buccia105/unity_game_controller/IMAGES/IMG_1095.JPG

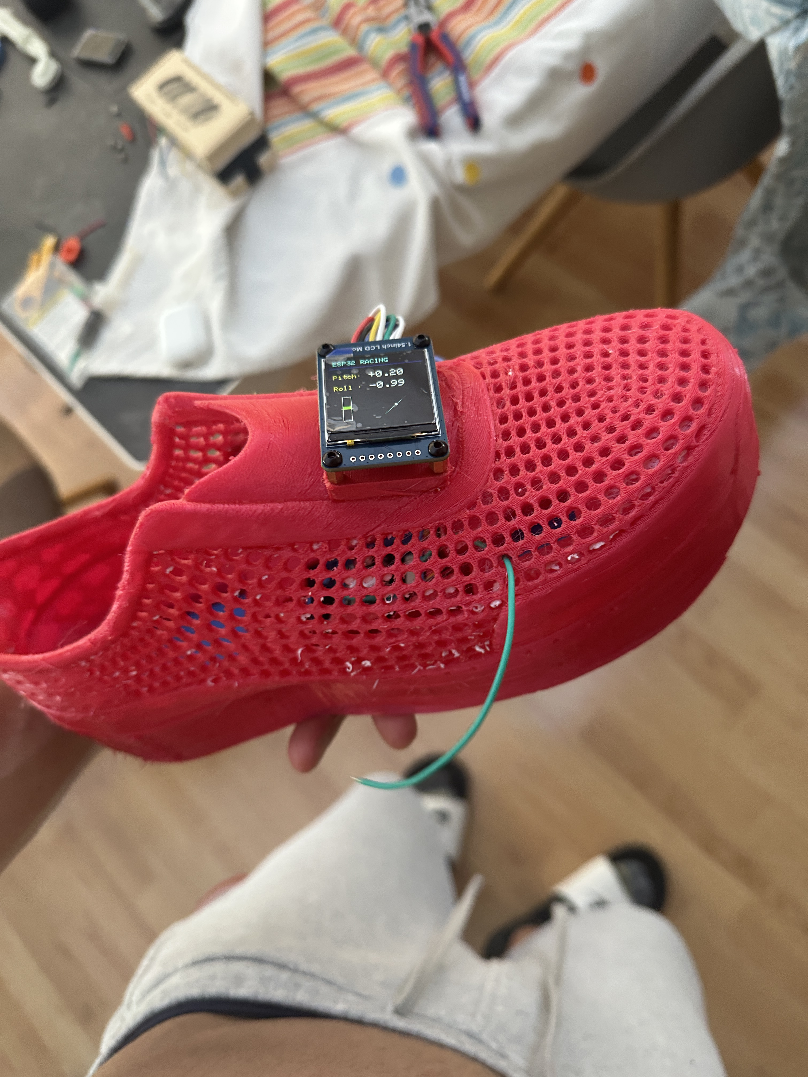
IMAGES/IMG_1095.JPG
