buccia105/unity_game_controller/include/template_credentials.h

#ifndef CREDENTIALS_H
#define CREDENTIALS_H

#define SECRET_WIFI_SSID "SSID" // access point name
#define SECRET_WIFI_PASS "PASSWORD" // access point password

#define UNITY_IP "192.168.xxx.xxx" // computer hosting the game ip
#define UNITY_PORT 7000 // osc_port (Do NOT change)

#endif
